Real-Time-Kodi/EuroServerRack/RackCabinets/RaspberryPi34ModelB/pi4_front.stl

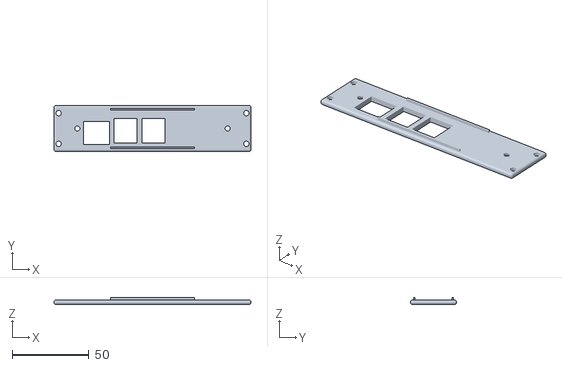
[picture p15: CAD file, 2024-05-09]
RackCabinets/RaspberryPi34ModelB/pi4_front.stl
128.5 x 30.0 x 4.50
