Real-Time-Kodi/EuroServerRack/RackCabinets/JetsonNano/jetson_lid.stl

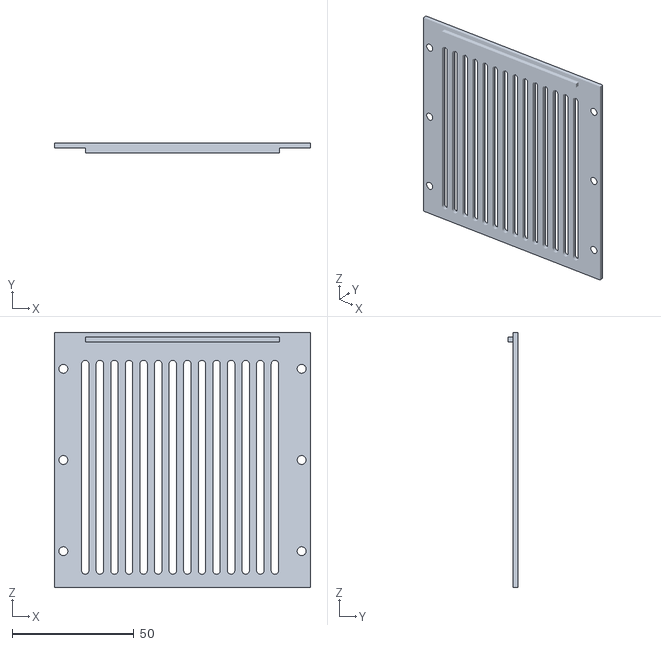
[picture p16: CAD file, 2024-05-06]
RackCabinets/JetsonNano/jetson_lid.stl
105.3 x 4.00 x 105.0
