Real-Time-Kodi/EuroServerRack/RackCabinets/RaspberryPi34ModelB/pi_backplate_molex.stl

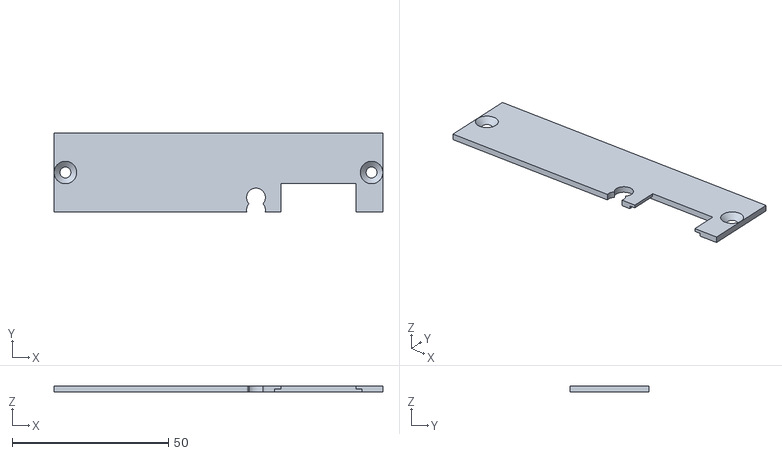
[picture p17: CAD file, 2024-05-09]
RackCabinets/RaspberryPi34ModelB/pi_backplate_molex.stl
105.3 x 25.3 x 2.00
