Real-Time-Kodi/EuroServerRack/RackCabinets/PDU/Holddown.FCStd

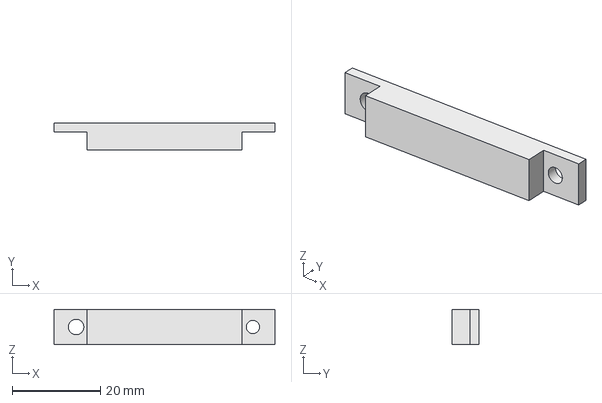
[picture p18: CAD file, 2024-05-09]
RackCabinets/PDU/Holddown.FCStd
50.0 x 6.00 x 8.00 mm
