Real-Time-Kodi/EuroServerRack/RackCabinets/RaspberryPi34ModelB/pi_chassis.stl

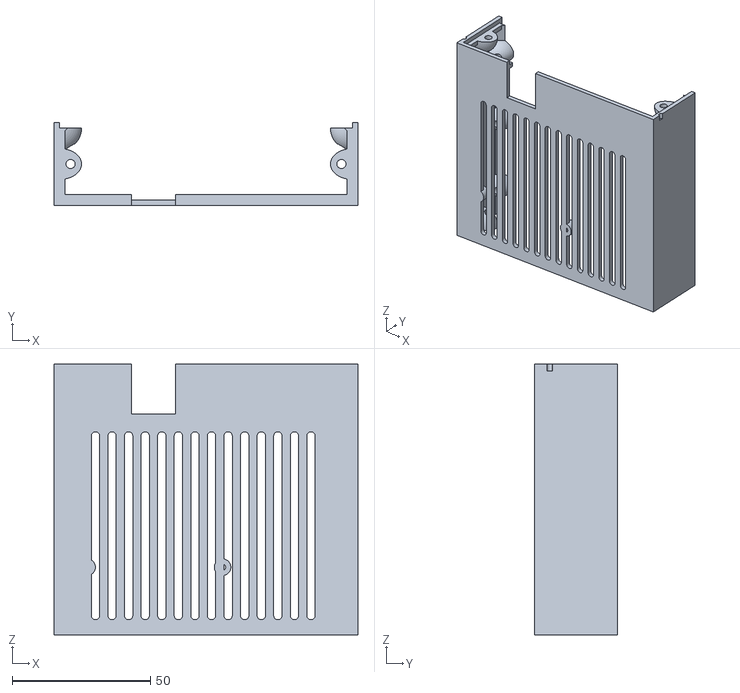
[picture p19: CAD file, 2024-05-09]
RackCabinets/RaspberryPi34ModelB/pi_chassis.stl
110.0 x 30.0 x 98.0
